e154/smart-home-socket/socket/socket.h

//
// Created by delta54 on 9/30/16.
//

#include <stdbool.h>
#include "../config.h"

#ifndef CMAKE_AVR_SOCKET_H
#define CMAKE_AVR_SOCKET_H

char buffer[10];
bool alert;
bool phase;
u16 current_temp;
u08 phase_counter;

void AlertBuzzer(void);
void SocketInit();
void Loop(void);

inline void EnableSocket() {
  output_high(TOGGLE_PORT, TOGGLE_PIN);
}

inline void DisableSocket() {
  output_low(TOGGLE_PORT, TOGGLE_PIN);
}

#endif //CMAKE_AVR_SOCKET_H
